rickymedrano/srirs-sensor-project/Pictures/foxTiled.png

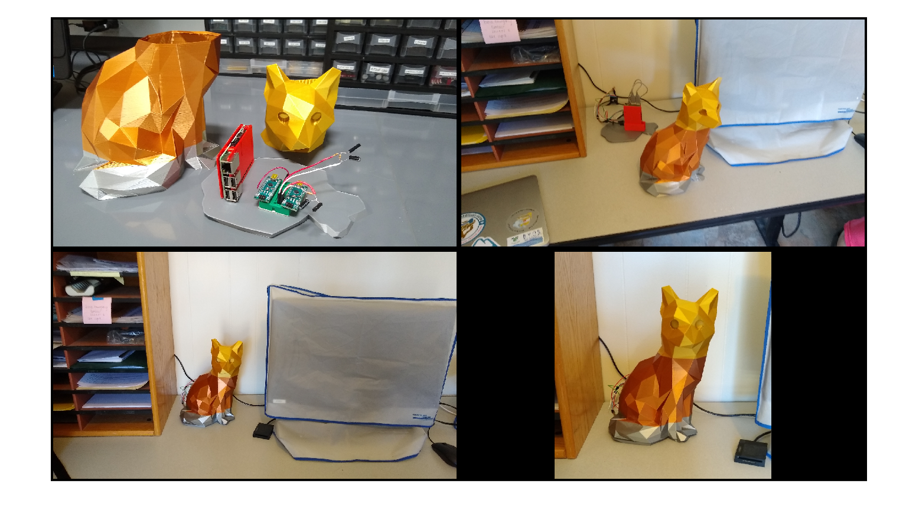
Pictures/foxTiled.png
