rickymedrano/srirs-sensor-project/Pictures/RandJ.jpg

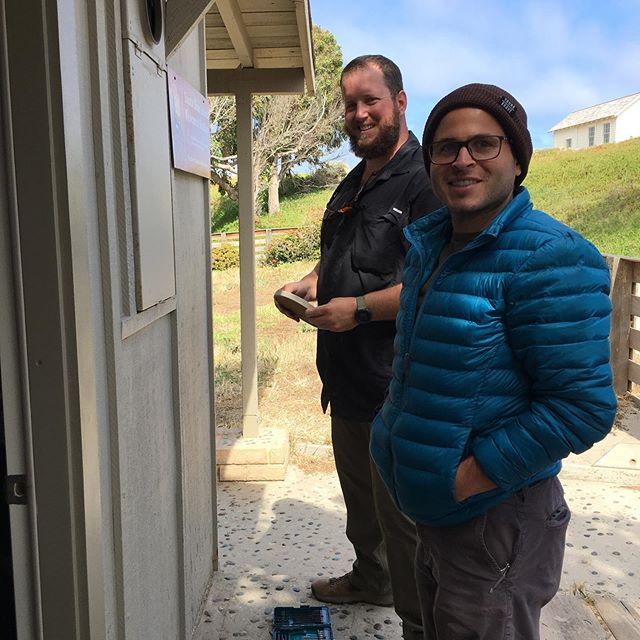
Pictures/RandJ.jpg
