rickymedrano/srirs-sensor-project/Pictures/waterTiled.png

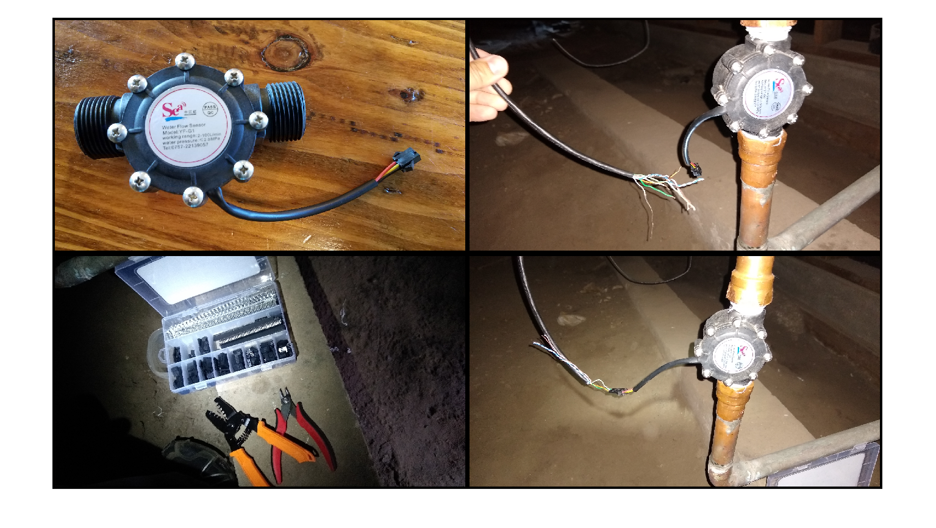
Pictures/waterTiled.png
